JimKnopfIoT/DER-DE-5000-IR-UART-TTL-Adapter/IMG_20251109_134327.jpg

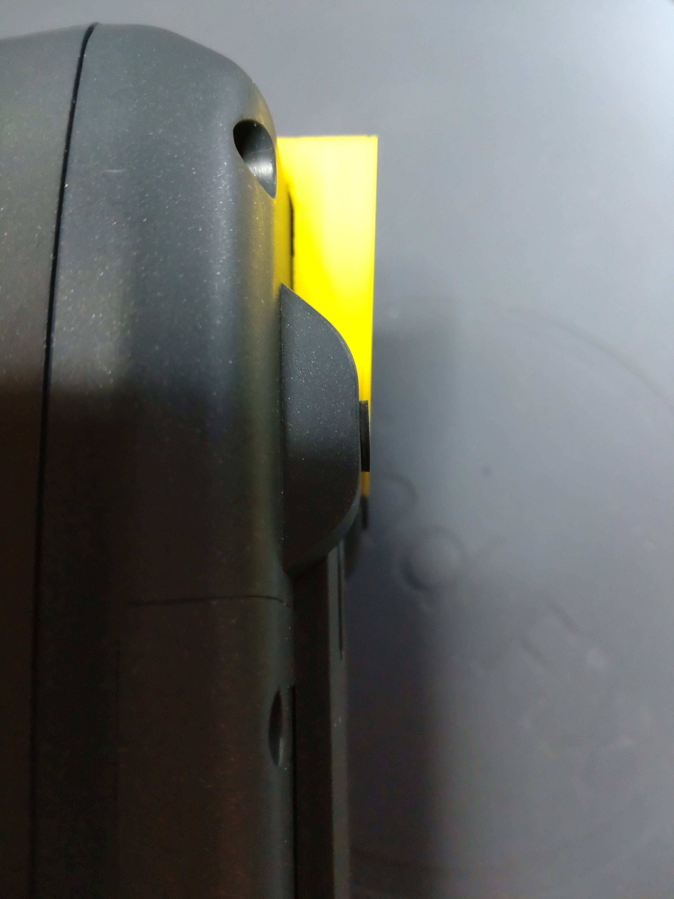
IMG_20251109_134327.jpg
