JimKnopfIoT/DER-DE-5000-IR-UART-TTL-Adapter/ViewCapture20251109_140654.png

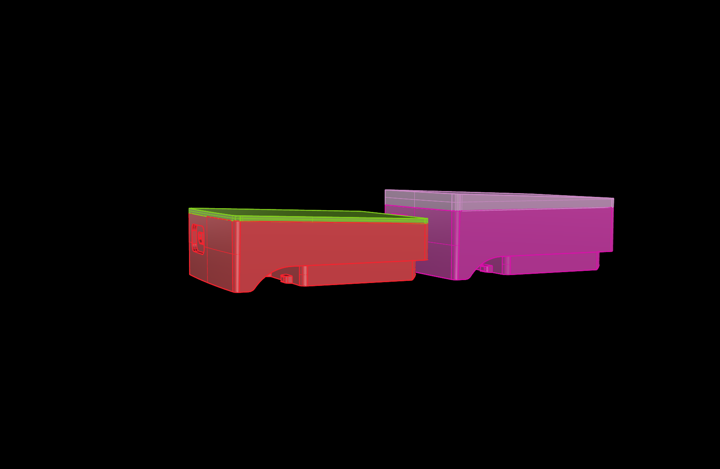
ViewCapture20251109_140654.png
